kishansheladiya/Design-and-Optimization-of-3D-Printed-Lattice-Structure-to-Enhance-Heat-Dissipation/Unitcell/BC star tetrahedron/front.PNG

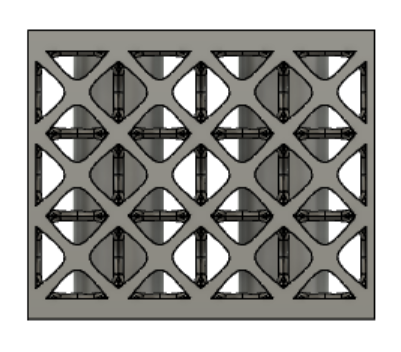
Unitcell/BC star tetrahedron/front.PNG
