kishansheladiya/Design-and-Optimization-of-3D-Printed-Lattice-Structure-to-Enhance-Heat-Dissipation/Unitcell/BC star tetrahedron/isometric.PNG

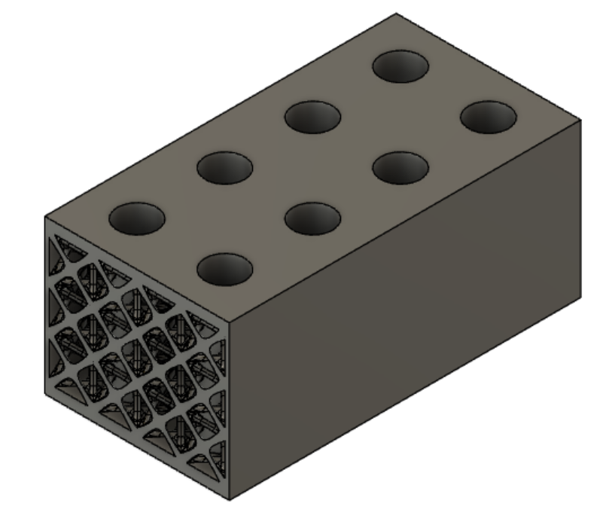
Unitcell/BC star tetrahedron/isometric.PNG
