kishansheladiya/Design-and-Optimization-of-3D-Printed-Lattice-Structure-to-Enhance-Heat-Dissipation/Unitcell/BC star tetrahedron/star tetrahedron algorithem.png

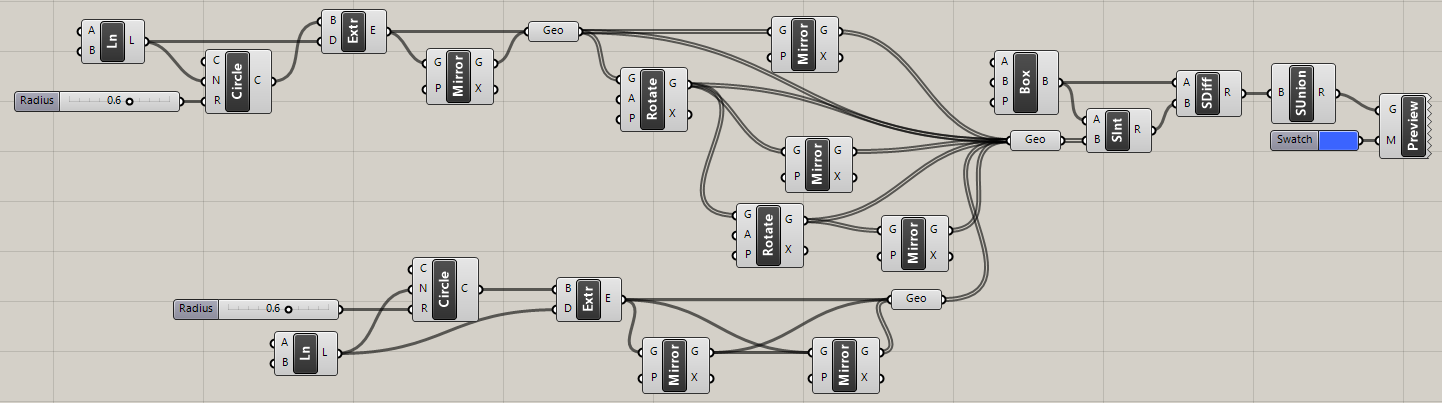
Unitcell/BC star tetrahedron/star tetrahedron algorithem.png
