kishansheladiya/Design-and-Optimization-of-3D-Printed-Lattice-Structure-to-Enhance-Heat-Dissipation/Unitcell/Bezier curve/bezier curve.jpg

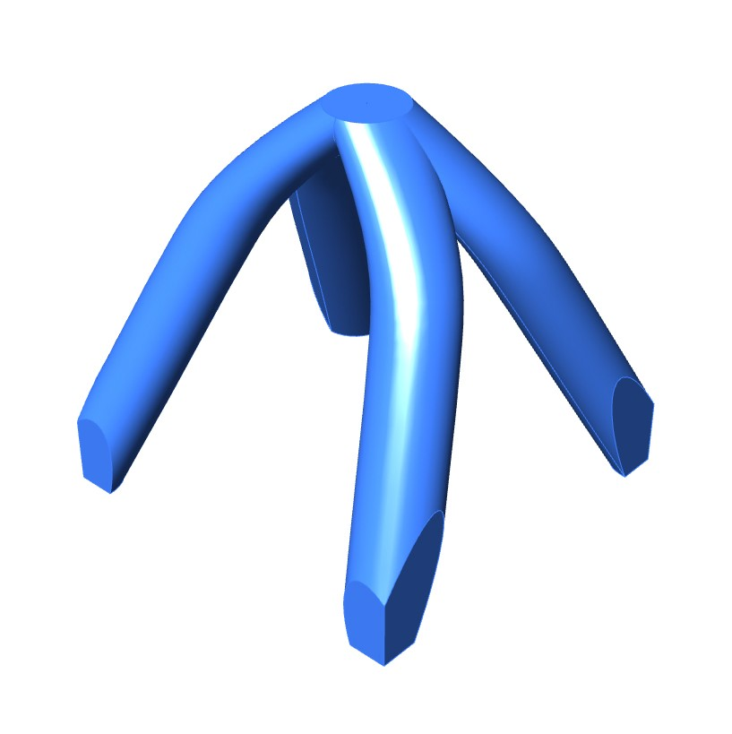
Unitcell/Bezier curve/bezier curve.jpg
