kishansheladiya/Design-and-Optimization-of-3D-Printed-Lattice-Structure-to-Enhance-Heat-Dissipation/Unitcell/Bezier curve/front.PNG

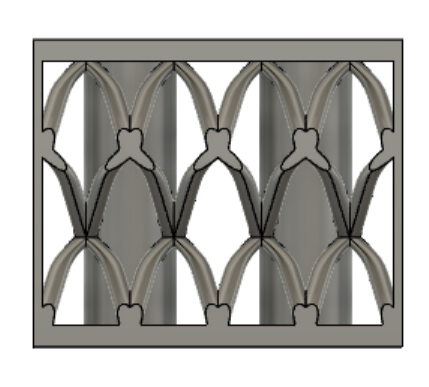
Unitcell/Bezier curve/front.PNG
