kishansheladiya/Design-and-Optimization-of-3D-Printed-Lattice-Structure-to-Enhance-Heat-Dissipation/Unitcell/Bezier curve/isometric.PNG

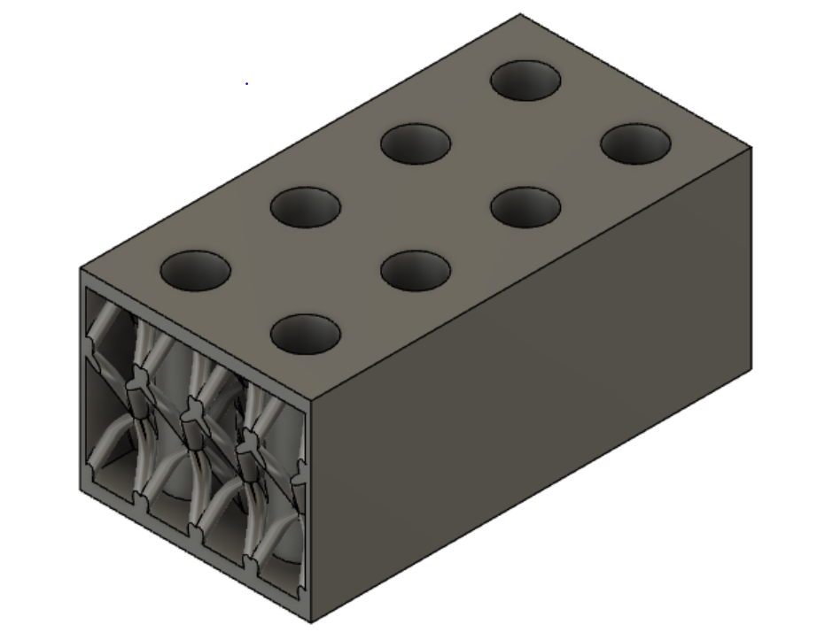
Unitcell/Bezier curve/isometric.PNG
