kishansheladiya/Design-and-Optimization-of-3D-Printed-Lattice-Structure-to-Enhance-Heat-Dissipation/Unitcell/Bezier curve/section.PNG

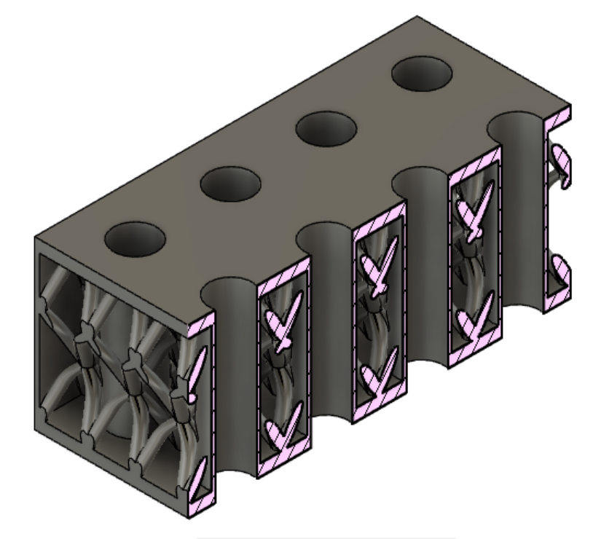
Unitcell/Bezier curve/section.PNG
