kishansheladiya/Design-and-Optimization-of-3D-Printed-Lattice-Structure-to-Enhance-Heat-Dissipation/Unitcell/Dedecahedron/dodecahedron algorithem.png

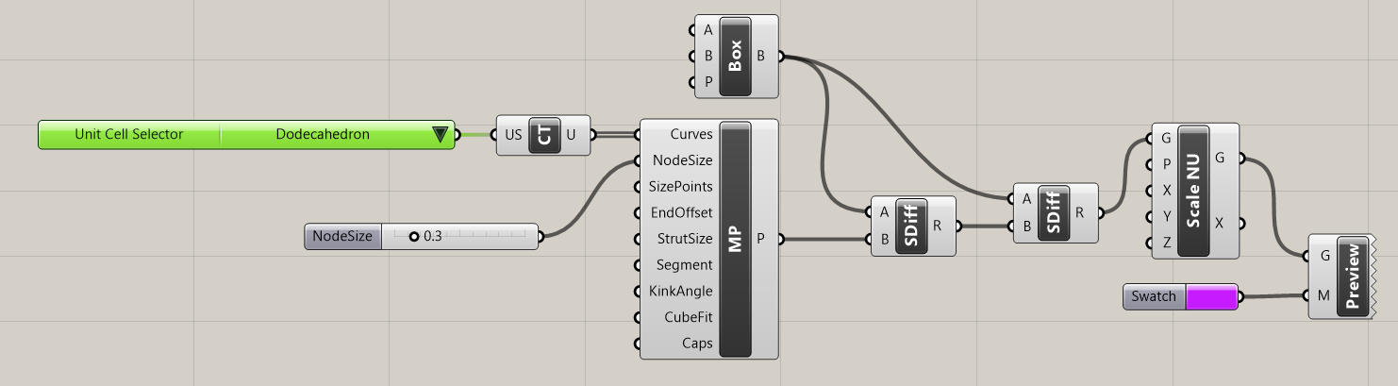
Unitcell/Dedecahedron/dodecahedron algorithem.png
