kishansheladiya/Design-and-Optimization-of-3D-Printed-Lattice-Structure-to-Enhance-Heat-Dissipation/Unitcell/Dedecahedron/section.PNG

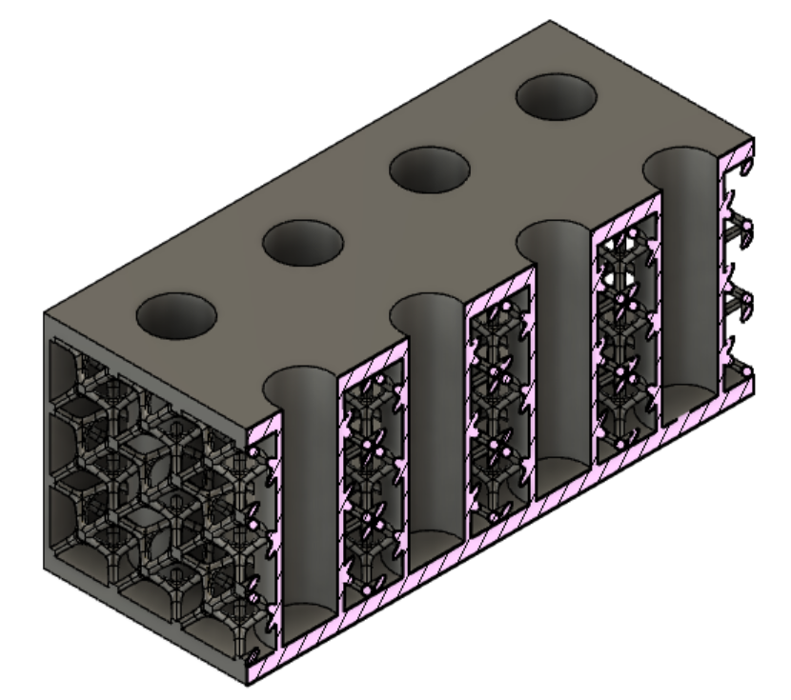
Unitcell/Dedecahedron/section.PNG
