kishansheladiya/Design-and-Optimization-of-3D-Printed-Lattice-Structure-to-Enhance-Heat-Dissipation/Unitcell/Tricut structure/section.PNG

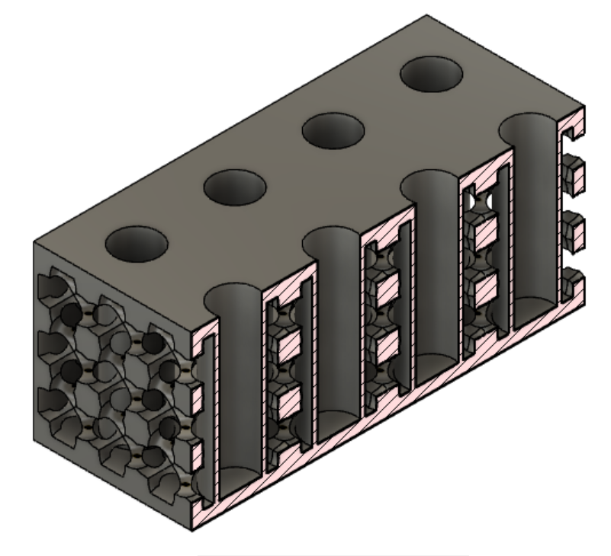
Unitcell/Tricut structure/section.PNG
