kishansheladiya/Design-and-Optimization-of-3D-Printed-Lattice-Structure-to-Enhance-Heat-Dissipation/Unitcell/Tricut structure/unit cell view.PNG

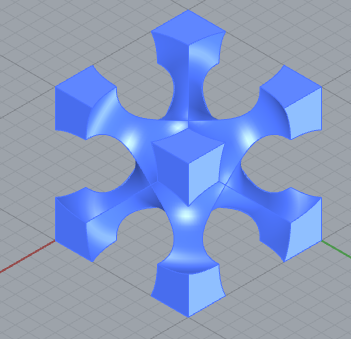
Unitcell/Tricut structure/unit cell view.PNG
